LosBagros/room-monitoring-device/img/1.jpg

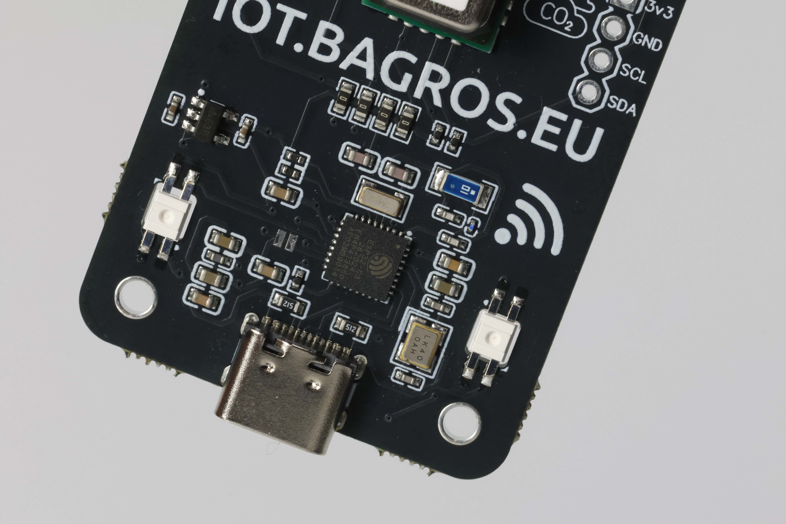
img/1.jpg
