LosBagros/room-monitoring-device/img/2.jpg

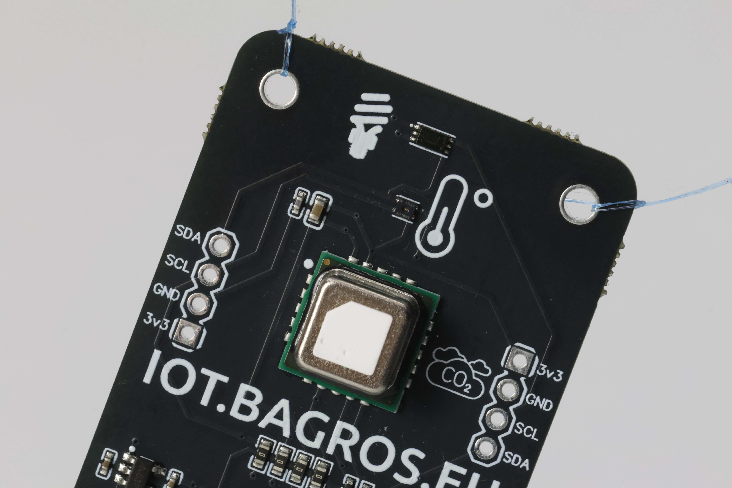
img/2.jpg
